lab11/torch/contiki/apps/coap/coap.c

#include "contiki-net.h"
#include "contiki.h"
#include "cpu.h"
#include "sys/etimer.h"
#include "sys/rtimer.h"
#include "dev/leds.h"
#include "dev/uart.h"
#include "dev/watchdog.h"
#include "dev/serial-line.h"
#include "dev/sys-ctrl.h"
#include "dev/pwm.h"
#include "sst25vf.h"
#include "net/rime/broadcast.h"
#include "net/ip/uip.h"
#include "net/ip/uip-udp-packet.h"
#include "net/ip/uiplib.h"
#include "net/ipv6/uip-ds6-route.h"
#include "net/ipv6/uip-ds6-nbr.h"
#include <stdio.h>
#include <stdint.h>
#include <stdlib.h>
#include "rest-engine.h"

#include "nrf51822.h"


#define SW_VERSION "1.2"
#define HW_VERSION "A"


PROCESS(app, "SDL Torch with CoAP");

PROCESS(fade_process, "Issue CoAP POST");
uint32_t fade_dc_start;
uint32_t fade_dc_stop;
uint8_t  fade_dc_direction;



AUTOSTART_PROCESSES(&app);


#define MAGIC 0x98cc431c

#ifndef DEFAULT_LIGHT_ON
#define DEFAULT_LIGHT_ON   0
#endif
#ifndef DEFAULT_LIGHT_FREQ
#define DEFAULT_LIGHT_FREQ 2000   // 2 kHz
#endif
#ifndef DEFAULT_LIGHT_DC
#define DEFAULT_LIGHT_DC   5000     // 50%
#endif

typedef struct {
  uint32_t magic;
  uint32_t light_on;
  uint32_t light_freq;
  uint32_t light_dc;
} torch_config_flash_t;

// State of the system that should be preserved
torch_config_flash_t torch_config;

static struct etimer fade_timer;

static void read_flash_config (torch_config_flash_t* conf) {
  sst25vf_read_page(0, (uint8_t*) conf, sizeof(torch_config_flash_t));
}

static void write_flash_config (torch_config_flash_t* conf) {
  // NOTE
  // we are erasing the first 4 kb each time, so don't put anything there
  sst25vf_4kb_erase(0);
  sst25vf_program(0, (uint8_t*) conf, sizeof(torch_config_flash_t));
}


static void
light_new_duty_cycle (uint32_t start, uint32_t dc)
{
  fade_dc_start = start;
  fade_dc_stop = dc;
  process_start(&fade_process, NULL);
}

static void
light_init () {
  pwm_init(GPTIMER_2, GPTIMER_SUBTIMER_A, torch_config.light_freq, torch_config.light_dc, LED_PWM_PORT_NUM, LED_PWM_PIN);
  pwm_start(GPTIMER_2, GPTIMER_SUBTIMER_A);

  // turn the light off if it should be off
  //    just setting the duty cycle to 0 doesn't work for some reason...
  if (!torch_config.light_on) {
      light_new_duty_cycle(torch_config.light_dc, 0);
  }
}

static void
light_set_on ()
{
  if (torch_config.light_on) return;
  torch_config.light_on = 1;
  light_new_duty_cycle(0, torch_config.light_dc);

  write_flash_config(&torch_config);
}

static void
light_set_off ()
{
  if (!torch_config.light_on) return;
  torch_config.light_on = 0;
  light_new_duty_cycle(torch_config.light_dc, 0);
  write_flash_config(&torch_config);
}


static void
light_set_frequency (uint32_t freq)
{
  torch_config.light_freq = freq;
  pwm_set_frequency(GPTIMER_2, GPTIMER_SUBTIMER_A, freq);
  write_flash_config(&torch_config);
}

static void
light_set_dc (uint32_t dc)
{
  uint32_t starting_dc;

  if (dc == 0) {
    light_set_off();
  } else {
    if (dc > 100) {
      dc = 100;
    }

    // Need to fix things up if dc == 0
    if (torch_config.light_on == 0) {
      starting_dc = 0;
      torch_config.light_on = 1;
    } else {
      starting_dc = torch_config.light_dc;
    }

    torch_config.light_dc = dc;
    light_new_duty_cycle(starting_dc, dc);
    write_flash_config(&torch_config);
  }
}




#define TO_CHAR(X) (((X) < 10) ? ('0' + (X)) : ('a' + ((X) - 10)))
int inet_ntop6 (const uip_ipaddr_t *addr, char *buf, int cnt) {
  uint16_t block, block2;
  char *end = buf + cnt;
  int i, j, compressed = 0;

  for (j = 0; j < 8; j++) {
    if (buf > end - 8)
      goto done;

    //block = ntohs(addr->s6_addr16[j]);
    block = (addr->u8[j*2] << 8) + addr->u8[(j*2) + 1];
    block2 = block;
    for (i = 4; i <= 16; i+=4) {
      if (block > (0xffff >> i) || (compressed == 2 && i == 16)) {
        *buf++ = TO_CHAR((block >> (16 - i)) & 0xf);
      }
    }
    if (block2 == 0 && compressed == 0) {
      *buf++ = ':';
      compressed++;
    }
    if (block2 != 0 && compressed == 1) compressed++;

    if (j < 7 && compressed != 1) *buf++ = ':';
  }
  if (compressed == 1)
    *buf++ = ':';
 done:
  *buf++ = '\0';
  return buf - (end - cnt);
}


int
coap_parse_bool (void* request)
{
  int length;
  const char* payload = NULL;

  length = REST.get_request_payload(request, (const uint8_t**) &payload);
  if (length > 0) {
    if (strncmp(payload, "true", length) == 0) {
      return 1;
    } else if (strncmp(payload, "false", length) == 0) {
      return 0;
    } else {
      return -1;
    }
  } else {
    return -1;
  }
}

int
coap_parse_uint (void* request, uint32_t* u)
{
  int length;
  const char* payload = NULL;

  length = REST.get_request_payload(request, (const uint8_t**) &payload);

  if (length > 0) {
    *u = strtol(payload, NULL, 10);
    return 0;
  }

  return -1;
}



/*******************************************************************************
 * onoff/Power
 ******************************************************************************/

static void
onoff_power_get_handler(void *request,
                  void *response,
                  uint8_t *buffer,
                  uint16_t preferred_size,
                  int32_t *offset) {
  int length;

  length = snprintf((char*) buffer, REST_MAX_CHUNK_SIZE, "%s", (torch_config.light_on)?"true":"false");

  REST.set_header_content_type(response, REST.type.TEXT_PLAIN);
  REST.set_response_payload(response, buffer, length);
}

static void
onoff_power_post_handler(void *request,
                  void *response,
                  uint8_t *buffer,
                  uint16_t preferred_size,
                  int32_t *offset) {

  int b = coap_parse_bool(request);
  if (b == 1) {
    light_set_on();
  } else if (b == 0) {
    light_set_off();
  } else {
    REST.set_response_status(response, REST.status.BAD_REQUEST);
  }
}

RESOURCE(coap_onoff_power,
         "title=\"onoffdevice/Power\";rt=\"Light\"",
         onoff_power_get_handler,
         onoff_power_post_handler,
         onoff_power_post_handler,
         NULL);


/*******************************************************************************
 * led0/Power
 ******************************************************************************/

static void
led_get_handler(void *request,
                void *response,
                uint8_t *buffer,
                uint16_t preferred_size,
                int32_t *offset,
                unsigned char led) {
  int length;

  length = snprintf((char*) buffer, REST_MAX_CHUNK_SIZE, "%s",
    ((leds_get()&led)==led)?"true":"false");

  REST.set_header_content_type(response, REST.type.TEXT_PLAIN);
  REST.set_response_payload(response, buffer, length);
}

static void
led_post_handler(void *request,
                 void *response,
                 uint8_t *buffer,
                 uint16_t preferred_size,
                 int32_t *offset,
                 unsigned char led) {
  uint8_t b = coap_parse_bool(request);
  if (b == 1) {
    leds_on(led);
  } else if (b == 0) {
    leds_off(led);
  } else {
    REST.set_response_status(response, REST.status.BAD_REQUEST);
  }

  // Update the nRF51822 state
  nRF51822_set_led_state(leds_get());
}

static void
led0_power_get_handler(void *request, void *response, uint8_t *buffer,
                       uint16_t preferred_size, int32_t *offset) {
  led_get_handler(request, response, buffer, preferred_size, offset, LEDS_GREEN);
}

static void
led0_power_post_handler(void *request, void *response, uint8_t *buffer,
                        uint16_t preferred_size, int32_t *offset) {
  led_post_handler(request, response, buffer, preferred_size, offset, LEDS_GREEN);
}

/* A simple actuator example. Toggles the red led */
RESOURCE(coap_led0_power,
         "title=\"Green LED\";rt=\"Control\"",
         led0_power_get_handler,
         led0_power_post_handler,
         led0_power_post_handler,
         NULL);


/*******************************************************************************
 * led1/Power
 ******************************************************************************/

static void
led1_power_get_handler(void *request, void *response, uint8_t *buffer,
                       uint16_t preferred_size, int32_t *offset) {
  led_get_handler(request, response, buffer, preferred_size, offset, LEDS_RED);
}

static void
led1_power_post_handler(void *request, void *response, uint8_t *buffer,
                        uint16_t preferred_size, int32_t *offset) {
  led_post_handler(request, response, buffer, preferred_size, offset, LEDS_RED);
}

/* A simple actuator example. Toggles the red led */
RESOURCE(coap_led1_power,
         "title=\"Red LED\";rt=\"Control\"",
         led1_power_get_handler,
         led1_power_post_handler,
         led1_power_post_handler,
         NULL);


/*******************************************************************************
 * led2/Power
 ******************************************************************************/

static void
led2_power_get_handler(void *request, void *response, uint8_t *buffer,
                       uint16_t preferred_size, int32_t *offset) {
  led_get_handler(request, response, buffer, preferred_size, offset, LEDS_BLUE);
}

static void
led2_power_post_handler(void *request, void *response, uint8_t *buffer,
                        uint16_t preferred_size, int32_t *offset) {
  led_post_handler(request, response, buffer, preferred_size, offset, LEDS_BLUE);
}

/* A simple actuator example. Toggles the red led */
RESOURCE(coap_led2_power,
         "title=\"Orange LED\";rt=\"Control\"",
         led2_power_get_handler,
         led2_power_post_handler,
         led2_power_post_handler,
         NULL);

/*******************************************************************************
 * sdl/luxapose/Frequency
 ******************************************************************************/

static void
sdl_luxapose_frequency_get_handler(void *request,
                  void *response,
                  uint8_t *buffer,
                  uint16_t preferred_size,
                  int32_t *offset) {
  int length;

read_flash_config(&torch_config);

  length = snprintf((char*) buffer, REST_MAX_CHUNK_SIZE, "%u", (unsigned int) torch_config.light_freq);

  REST.set_header_content_type(response, REST.type.TEXT_PLAIN);
  REST.set_response_payload(response, buffer, length);
}

static void
sdl_luxapose_frequency_post_handler(void *request,
                  void *response,
                  uint8_t *buffer,
                  uint16_t preferred_size,
                  int32_t *offset) {

  uint32_t u;
  int ret;

  ret = coap_parse_uint(request, &u);
  if (ret < 0) {
    REST.set_response_status(response, REST.status.BAD_REQUEST);
  } else {
    light_set_frequency(u);
  }
}

RESOURCE(coap_sdl_luxapose_frequency,
         "title=\"Luxapose Frequency\"",
         sdl_luxapose_frequency_get_handler,
         sdl_luxapose_frequency_post_handler,
         sdl_luxapose_frequency_post_handler,
         NULL);

/*******************************************************************************
 * sdl/luxapose/DutyCycle
 ******************************************************************************/

static void
sdl_luxapose_dutycycle_get_handler(void *request,
                  void *response,
                  uint8_t *buffer,
                  uint16_t preferred_size,
                  int32_t *offset) {
  int length;

read_flash_config(&torch_config);

  length = snprintf((char*) buffer, REST_MAX_CHUNK_SIZE, "%u", (unsigned int) torch_config.light_dc/100);

  REST.set_header_content_type(response, REST.type.TEXT_PLAIN);
  REST.set_response_payload(response, buffer, length);
}

static void
sdl_luxapose_dutycycle_post_handler(void *request,
                  void *response,
                  uint8_t *buffer,
                  uint16_t preferred_size,
                  int32_t *offset) {

  uint32_t u;
  int ret;

  ret = coap_parse_uint(request, &u);
  if (ret < 0) {
    REST.set_response_status(response, REST.status.BAD_REQUEST);
  } else {
    light_set_dc(u*100);
  }
}

RESOURCE(coap_sdl_luxapose_dutycycle,
         "title=\"Luxapose Duty Cycle (todo)\"",
         sdl_luxapose_dutycycle_get_handler,
         sdl_luxapose_dutycycle_post_handler,
         sdl_luxapose_dutycycle_post_handler,
         NULL);



/*******************************************************************************
 * device/software/Version
 ******************************************************************************/

static void
device_software_version_get_handler(void *request,
                  void *response,
                  uint8_t *buffer,
                  uint16_t preferred_size,
                  int32_t *offset) {
  int length;
  char res[] = "%s";

  length = snprintf((char*) buffer, REST_MAX_CHUNK_SIZE, res, SW_VERSION);

  REST.set_header_content_type(response, REST.type.TEXT_PLAIN);
  REST.set_response_payload(response, buffer, length);
}

RESOURCE(coap_device_software_version,
         "title=\"device/software/Version\";rt=\"sw\"",
         device_software_version_get_handler,
         NULL,
         NULL,
         NULL);


/*******************************************************************************
 * device/hardware/Version
 ******************************************************************************/

static void
device_hardware_version_get_handler(void *request,
                  void *response,
                  uint8_t *buffer,
                  uint16_t preferred_size,
                  int32_t *offset) {
  int length;
  char res[] = "%s";

  length = snprintf((char*) buffer, REST_MAX_CHUNK_SIZE, res, HW_VERSION);

  REST.set_header_content_type(response, REST.type.TEXT_PLAIN);
  REST.set_response_payload(response, buffer, length);
}

RESOURCE(coap_device_hardware_version,
         "title=\"device/hardware/Version\";rt=\"hw\"",
         device_hardware_version_get_handler,
         NULL,
         NULL,
         NULL);


/*******************************************************************************
 * Interface with the nRF51822
 ******************************************************************************/

void handle_ble_interrupt (uint8_t type, uint8_t len, uint8_t* buf) {
  if (type == BCP_RSP_LED && len == 1) {
    leds_arch_set(buf[0]);

  } else if (type == BCP_RSP_WHITE_LIGHT) {
    light_set_dc(buf[0]);
  }
}





PROCESS_THREAD(app, ev, data) {
  PROCESS_BEGIN();

  leds_on(LEDS_ALL);

  // Check the flash for a saved config blob
  // And init the main LED
  {
    read_flash_config(&torch_config);

    if (torch_config.magic != MAGIC) {
      // Give it an ol erase for good measure
      sst25vf_chip_erase();

      // Setup defaults
      torch_config.magic      = MAGIC;
      torch_config.light_on   = DEFAULT_LIGHT_ON;
      torch_config.light_freq = DEFAULT_LIGHT_FREQ;
      torch_config.light_dc   = DEFAULT_LIGHT_DC;
      // Save them so we don't do this next time
      write_flash_config(&torch_config);
    }
    // Set the light to the saved values
    light_init();
  }

  // CoAP + REST
  rest_init_engine();

  rest_activate_resource(&coap_onoff_power,             "onoff/Power");

  rest_activate_resource(&coap_led0_power,              "led0/Power");
  rest_activate_resource(&coap_led1_power,              "led1/Power");
  rest_activate_resource(&coap_led2_power,              "led2/Power");

  rest_activate_resource(&coap_sdl_luxapose_frequency,  "sdl/luxapose/Frequency");
  rest_activate_resource(&coap_sdl_luxapose_dutycycle,  "sdl/luxapose/DutyCycle");

  rest_activate_resource(&coap_device_software_version, "device/software/Version");
  rest_activate_resource(&coap_device_hardware_version, "device/hardware/Version");


  // BLE
  nrf51822_init(handle_ble_interrupt);

  while (1) {
    PROCESS_WAIT_EVENT();
  }

  PROCESS_END();
}


/* This process handles making a fade between different light duty cycles.
 */
PROCESS_THREAD(fade_process, ev, data) {
  PROCESS_BEGIN();

  // All state is global because something is weird with these contiki macros

  // Need to record if we are going up or down
  if (fade_dc_start > fade_dc_stop) {
    fade_dc_direction = 0;
  } else {
    fade_dc_direction = 1;
  }

  etimer_set(&fade_timer, CLOCK_SECOND/500);

  while (1) {
    PROCESS_WAIT_EVENT();

    if (etimer_expired(&fade_timer)) {

      if (fade_dc_direction == 0) {
        fade_dc_start--;
      } else {
        fade_dc_start++;
      }

      pwm_set_dutycycle(GPTIMER_2, GPTIMER_SUBTIMER_A, fade_dc_start);
      leds_toggle(LEDS_GREEN);

      if ((fade_dc_direction == 0 && fade_dc_start > fade_dc_stop) ||
          (fade_dc_direction == 1 && fade_dc_start < fade_dc_stop)) {
        etimer_restart(&fade_timer);
      } else {
        break;
      }
    }
  }

  PROCESS_END();
}
